Enthusela/DesktopControlPanel/eink/bmp/test256colors.bmp

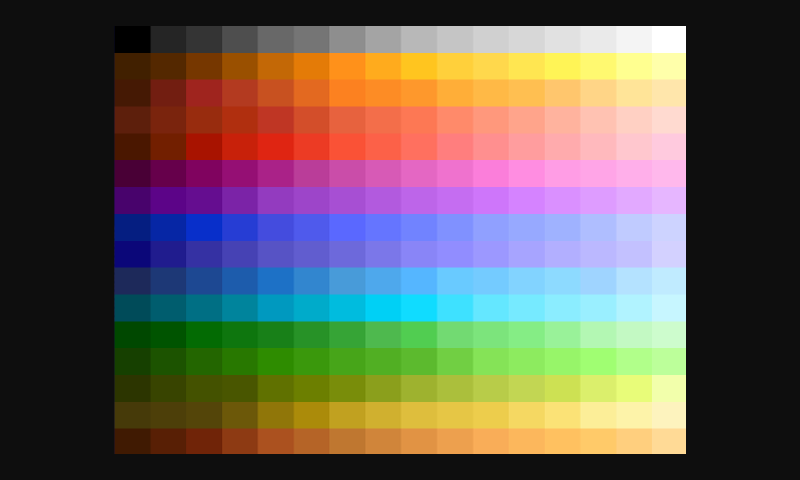
eink/bmp/test256colors.bmp
