Enthusela/DesktopControlPanel/eink/bmp/capture_nasa.bmp

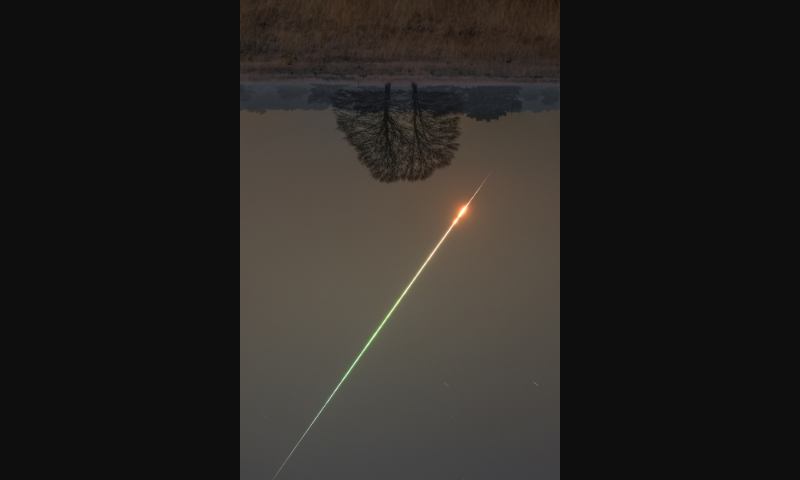
eink/bmp/capture_nasa.bmp
