Enthusela/DesktopControlPanel/eink/bmp/capture_nasa_quantized.bmp

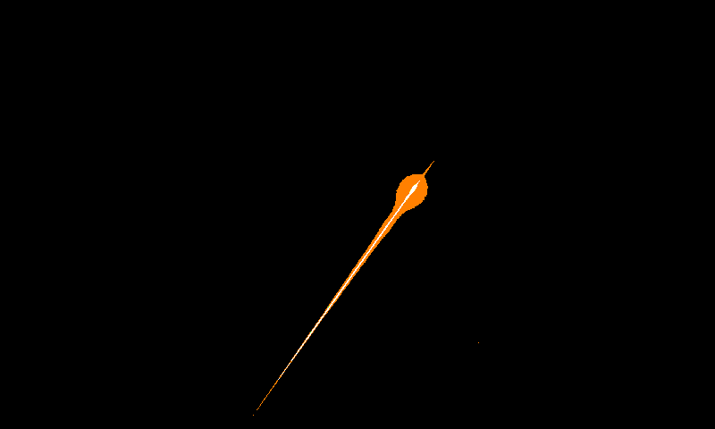
eink/bmp/capture_nasa_quantized.bmp
