Enthusela/DesktopControlPanel/eink/bmp/capture_wc.bmp

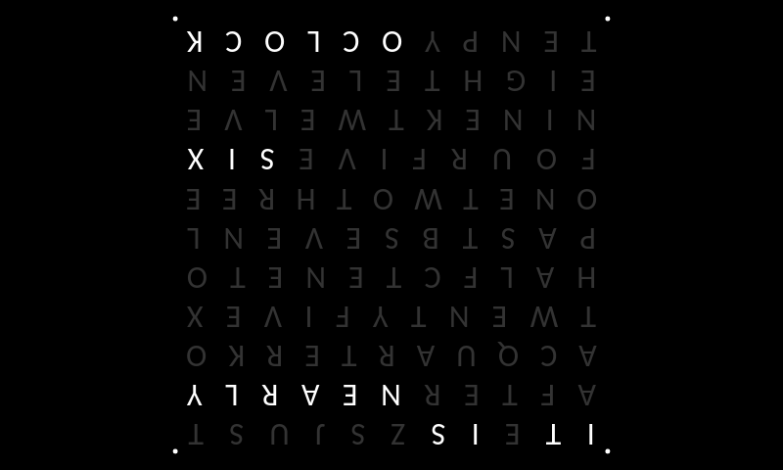
eink/bmp/capture_wc.bmp
