Enthusela/DesktopControlPanel/eink/bmp/world_map.bmp

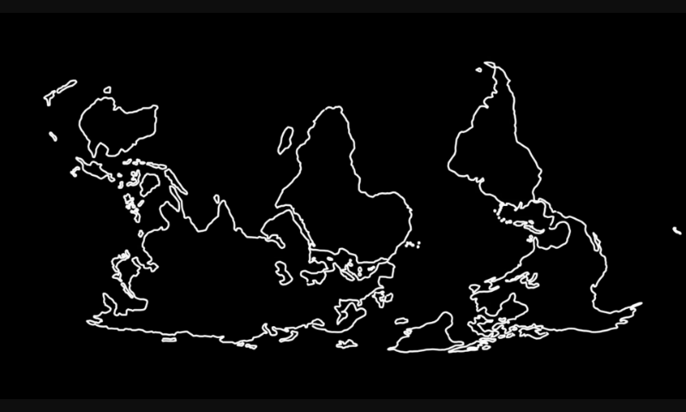
eink/bmp/world_map.bmp
