Enthusela/DesktopControlPanel/eink/png/capture_nasa.png

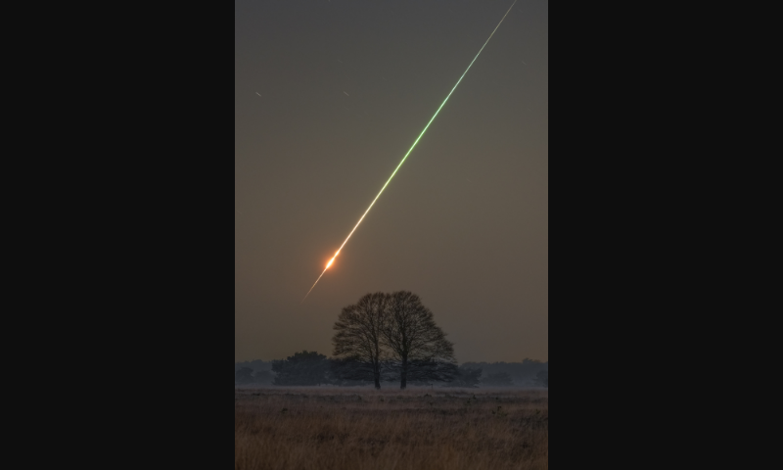
eink/png/capture_nasa.png
