Enthusela/DesktopControlPanel/eink/png/capture_wc.png

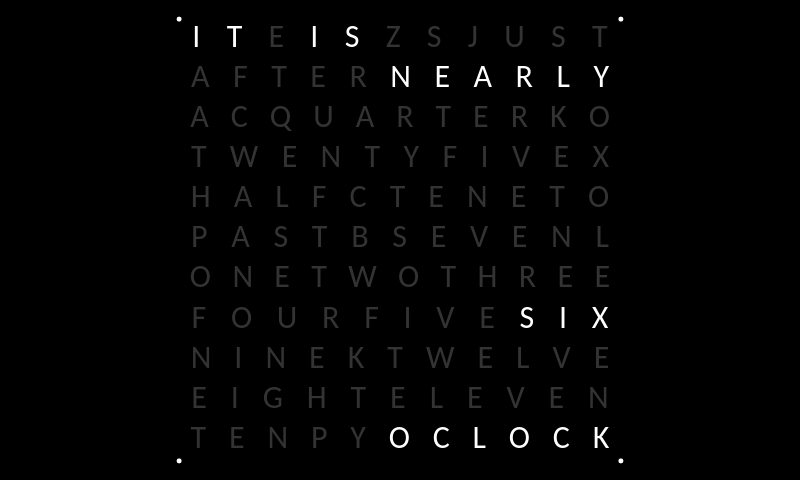
eink/png/capture_wc.png
