Enthusela/DesktopControlPanel/eink/png/world_map_resized.png

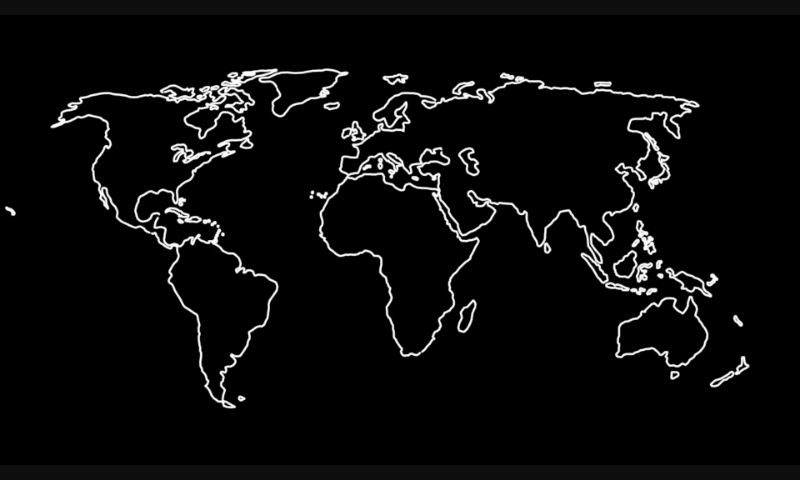
eink/png/world_map_resized.png
