Enthusela/DesktopControlPanel/eink/bmp/test256color_quantized.bmp

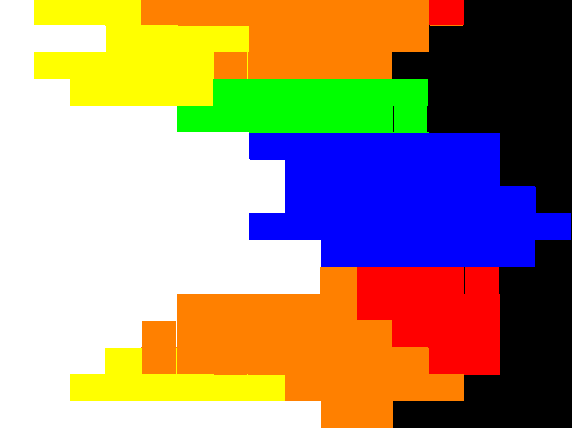
eink/bmp/test256color_quantized.bmp
