Enthusela/DesktopControlPanel/faceplate_ctrl/DesktopControlPanel.h

#ifndef DESKTOP_CONTROL_PANEL_H
#define DESKTOP_CONTROL_PANEL_H

#include "DCPDefines.h"
#include <Arduino.h>
#include <FastLED.h>
#include <chipsets.h>
#include <math.h>
#include <string.h>
#include <Wire.h>
#include <Adafruit_MotorShield.h>
#include "DCPMiscFunctions.h"
#include "DCPLightingFunctions.h"
#include "Potentiometer.h"
#include "SoftTakeoverLEDs.h"
#include "ControlPot.h"
#include "ToggleSwitch.h"

#endif
